johnkok/Amplifier/fw/Drivers/DISPLAY/tm_stm32f4_ili9341.c

/**	
 * |----------------------------------------------------------------------
 * | Copyright (C) Tilen Majerle, 2014
 * | 
 * | This program is free software: you can redistribute it and/or modify
 * | it under the terms of the GNU General Public License as published by
 * | the Free Software Foundation, either version 3 of the License, or
 * | any later version.
 * |  
 * | This program is distributed in the hope that it will be useful,
 * | but WITHOUT ANY WARRANTY; without even the implied warranty of
 * | MERCHANTABILITY or FITNESS FOR A PARTICULAR PURPOSE.  See the
 * | GNU General Public License for more details.
 * | 
 * | You should have received a copy of the GNU General Public License
 * | along with this program.  If not, see <http://www.gnu.org/licenses/>.
 * |----------------------------------------------------------------------
 */
#include "tm_stm32f4_ili9341.h"
#include "stm32f4xx_hal_gpio.h"

extern SPI_HandleTypeDef hspi1;
extern const struct {
  uint32_t   width;
  uint32_t   height;
  uint32_t   bytes_per_pixel; /* 2:RGB16, 3:RGB, 4:RGBA */
  uint8_t 	 pixel_data[];
} vu_image;

/**
 * @brief  Orientation
 * @note   Used private
 */
typedef enum {
	TM_ILI9341_Landscape,
	TM_ILI9341_Portrait
} TM_ILI9341_Orientation;

/**
 * @brief  LCD options
 * @note   Used private
 */
typedef struct {
	uint16_t width;
	uint16_t height;
	TM_ILI9341_Orientation orientation; // 1 = portrait; 0 = landscape
} TM_ILI931_Options_t;

/* Pin definitions */
#define ILI9341_RST_SET				HAL_GPIO_WritePin(ILI9341_RST_PORT, ILI9341_RST_PIN, 1)
#define ILI9341_RST_RESET			HAL_GPIO_WritePin(ILI9341_RST_PORT, ILI9341_RST_PIN, 0)
#define ILI9341_CS_SET				HAL_GPIO_WritePin(ILI9341_CS_PORT, ILI9341_CS_PIN, 1)
#define ILI9341_CS_RESET			HAL_GPIO_WritePin(ILI9341_CS_PORT, ILI9341_CS_PIN, 0)
#define ILI9341_WRX_SET				HAL_GPIO_WritePin(ILI9341_WRX_PORT, ILI9341_WRX_PIN, 1)
#define ILI9341_WRX_RESET			HAL_GPIO_WritePin(ILI9341_WRX_PORT, ILI9341_WRX_PIN, 0)
//#define ILI9341_BL_SET				HAL_GPIO_WritePin(ILI9341_BL_PORT, ILI9341_BL_PIN, 1)
//#define ILI9341_BL_RESET			HAL_GPIO_WritePin(ILI9341_BL_PORT, ILI9341_BL_PIN, 0)

/* Private defines */
#define ILI9341_RESET				0x01
#define ILI9341_SLEEP_OUT			0x11
#define ILI9341_GAMMA				0x26
#define ILI9341_DISPLAY_OFF			0x28
#define ILI9341_DISPLAY_ON			0x29
#define ILI9341_COLUMN_ADDR			0x2A
#define ILI9341_PAGE_ADDR			0x2B
#define ILI9341_GRAM				0x2C
#define ILI9341_MAC					0x36
#define ILI9341_PIXEL_FORMAT		0x3A
#define ILI9341_WDB					0x51
#define ILI9341_WCD					0x53
#define ILI9341_RGB_INTERFACE		0xB0
#define ILI9341_FRC					0xB1
#define ILI9341_BPC					0xB5
#define ILI9341_DFC					0xB6
#define ILI9341_POWER1				0xC0
#define ILI9341_POWER2				0xC1
#define ILI9341_VCOM1				0xC5
#define ILI9341_VCOM2				0xC7
#define ILI9341_POWERA				0xCB
#define ILI9341_POWERB				0xCF
#define ILI9341_PGAMMA				0xE0
#define ILI9341_NGAMMA				0xE1
#define ILI9341_DTCA				0xE8
#define ILI9341_DTCB				0xEA
#define ILI9341_POWER_SEQ			0xED
#define ILI9341_3GAMMA_EN			0xF2
#define ILI9341_INTERFACE			0xF6
#define ILI9341_PRC					0xF7

/* Pin functions */
uint16_t ILI9341_x;
uint16_t ILI9341_y;
TM_ILI931_Options_t ILI9341_Opts;
uint8_t ILI9341_INT_CalledFromPuts = 0;

/* Private functions */
void TM_ILI9341_InitLCD(void);
void TM_ILI9341_SendData(uint8_t data);
void TM_ILI9341_SendCommand(uint8_t data);
void TM_ILI9341_Delay(volatile unsigned int delay);
void TM_ILI9341_SetCursorPosition(uint16_t x1, uint16_t y1, uint16_t x2, uint16_t y2);
void TM_ILI9341_INT_Fill(uint16_t x0, uint16_t y0, uint16_t x1, uint16_t y1, uint16_t color);

void TM_ILI9341_Init() {
	
	/* Init LCD */
//	ILI9341_BL_RESET;

	TM_ILI9341_InitLCD();	
	
	/* Set default settings */
	ILI9341_x = ILI9341_y = 0;
	ILI9341_Opts.width = ILI9341_WIDTH;
	ILI9341_Opts.height = ILI9341_HEIGHT;
	ILI9341_Opts.orientation = TM_ILI9341_Portrait;

	TM_ILI9341_Rotate(TM_ILI9341_Orientation_Landscape_2);
	
	/* Fill with white color */
	TM_ILI9341_Fill(ILI9341_COLOR_BLACK);

//	ILI9341_BL_SET;
}

void TM_ILI9341_InitLCD(void) {
	/* Force reset */
	ILI9341_RST_RESET;
	TM_ILI9341_Delay(20000);
	ILI9341_RST_SET;
	
	/* Delay for RST response */
	TM_ILI9341_Delay(20000);
	
	/* Software reset */
	TM_ILI9341_SendCommand(ILI9341_RESET);
	TM_ILI9341_Delay(50000);
	
	TM_ILI9341_SendCommand(ILI9341_POWERA);
	TM_ILI9341_SendData(0x39);
	TM_ILI9341_SendData(0x2C);
	TM_ILI9341_SendData(0x00);
	TM_ILI9341_SendData(0x34);
	TM_ILI9341_SendData(0x02);
	TM_ILI9341_SendCommand(ILI9341_POWERB);
	TM_ILI9341_SendData(0x00);
	TM_ILI9341_SendData(0xC1);
	TM_ILI9341_SendData(0x30);
	TM_ILI9341_SendCommand(ILI9341_DTCA);
	TM_ILI9341_SendData(0x85);
	TM_ILI9341_SendData(0x00);
	TM_ILI9341_SendData(0x78);
	TM_ILI9341_SendCommand(ILI9341_DTCB);
	TM_ILI9341_SendData(0x00);
	TM_ILI9341_SendData(0x00);
	TM_ILI9341_SendCommand(ILI9341_POWER_SEQ);
	TM_ILI9341_SendData(0x64);
	TM_ILI9341_SendData(0x03);
	TM_ILI9341_SendData(0x12);
	TM_ILI9341_SendData(0x81);
	TM_ILI9341_SendCommand(ILI9341_PRC);
	TM_ILI9341_SendData(0x20);
	TM_ILI9341_SendCommand(ILI9341_POWER1);
	TM_ILI9341_SendData(0x23);
	TM_ILI9341_SendCommand(ILI9341_POWER2);
	TM_ILI9341_SendData(0x10);
	TM_ILI9341_SendCommand(ILI9341_VCOM1);
	TM_ILI9341_SendData(0x3E);
	TM_ILI9341_SendData(0x28);
	TM_ILI9341_SendCommand(ILI9341_VCOM2);
	TM_ILI9341_SendData(0x86);
	TM_ILI9341_SendCommand(ILI9341_MAC);
	TM_ILI9341_SendData(0x48);
	TM_ILI9341_SendCommand(ILI9341_PIXEL_FORMAT);
	TM_ILI9341_SendData(0x55);
	TM_ILI9341_SendCommand(ILI9341_FRC);
	TM_ILI9341_SendData(0x00);
	TM_ILI9341_SendData(0x18);
	TM_ILI9341_SendCommand(ILI9341_DFC);
	TM_ILI9341_SendData(0x08);
	TM_ILI9341_SendData(0x82);
	TM_ILI9341_SendData(0x27);
	TM_ILI9341_SendCommand(ILI9341_3GAMMA_EN);
	TM_ILI9341_SendData(0x00);
	TM_ILI9341_SendCommand(ILI9341_COLUMN_ADDR);
	TM_ILI9341_SendData(0x00);
	TM_ILI9341_SendData(0x00);
	TM_ILI9341_SendData(0x00);
	TM_ILI9341_SendData(0xEF);
	TM_ILI9341_SendCommand(ILI9341_PAGE_ADDR);
	TM_ILI9341_SendData(0x00);
	TM_ILI9341_SendData(0x00);
	TM_ILI9341_SendData(0x01);
	TM_ILI9341_SendData(0x3F);
	TM_ILI9341_SendCommand(ILI9341_GAMMA);
	TM_ILI9341_SendData(0x01);
	TM_ILI9341_SendCommand(ILI9341_PGAMMA);
	TM_ILI9341_SendData(0x0F);
	TM_ILI9341_SendData(0x31);
	TM_ILI9341_SendData(0x2B);
	TM_ILI9341_SendData(0x0C);
	TM_ILI9341_SendData(0x0E);
	TM_ILI9341_SendData(0x08);
	TM_ILI9341_SendData(0x4E);
	TM_ILI9341_SendData(0xF1);
	TM_ILI9341_SendData(0x37);
	TM_ILI9341_SendData(0x07);
	TM_ILI9341_SendData(0x10);
	TM_ILI9341_SendData(0x03);
	TM_ILI9341_SendData(0x0E);
	TM_ILI9341_SendData(0x09);
	TM_ILI9341_SendData(0x00);
	TM_ILI9341_SendCommand(ILI9341_NGAMMA);
	TM_ILI9341_SendData(0x00);
	TM_ILI9341_SendData(0x0E);
	TM_ILI9341_SendData(0x14);
	TM_ILI9341_SendData(0x03);
	TM_ILI9341_SendData(0x11);
	TM_ILI9341_SendData(0x07);
	TM_ILI9341_SendData(0x31);
	TM_ILI9341_SendData(0xC1);
	TM_ILI9341_SendData(0x48);
	TM_ILI9341_SendData(0x08);
	TM_ILI9341_SendData(0x0F);
	TM_ILI9341_SendData(0x0C);
	TM_ILI9341_SendData(0x31);
	TM_ILI9341_SendData(0x36);
	TM_ILI9341_SendData(0x0F);
	TM_ILI9341_SendCommand(ILI9341_SLEEP_OUT);

	TM_ILI9341_Delay(1000000);

	TM_ILI9341_SendCommand(ILI9341_DISPLAY_ON);
	TM_ILI9341_SendCommand(ILI9341_GRAM);
}

void TM_ILI9341_DisplayOn(void) {
	TM_ILI9341_SendCommand(ILI9341_DISPLAY_ON);
}

void TM_ILI9341_DisplayOff(void) {
	TM_ILI9341_SendCommand(ILI9341_DISPLAY_OFF);
}

void TM_ILI9341_SendCommand(uint8_t data) {
	ILI9341_WRX_RESET;
	ILI9341_CS_RESET;
	HAL_SPI_Transmit(&hspi1, &data, 1, 5);
	//HAL_SPI_Transmit_DMA(&hspi1, &data, 1);
	ILI9341_CS_SET;
}

void TM_ILI9341_SendData(uint8_t data) {
	ILI9341_WRX_SET;
	ILI9341_CS_RESET;
	HAL_SPI_Transmit(&hspi1, &data, 1, 5);
	//HAL_SPI_Transmit_DMA(&hspi1, &data, 1);
	ILI9341_CS_SET;
}

void TM_ILI9341_DrawPixel(uint16_t x, uint16_t y, uint32_t color) {
	TM_ILI9341_SetCursorPosition(x, y, x, y);

	TM_ILI9341_SendCommand(ILI9341_GRAM);
	TM_ILI9341_SendData(color >> 8);
	TM_ILI9341_SendData(color & 0xFF);
}


void TM_ILI9341_SetCursorPosition(uint16_t x1, uint16_t y1, uint16_t x2, uint16_t y2) {
	TM_ILI9341_SendCommand(ILI9341_COLUMN_ADDR);
	TM_ILI9341_SendData(x1 >> 8);
	TM_ILI9341_SendData(x1 & 0xFF);
	TM_ILI9341_SendData(x2 >> 8);
	TM_ILI9341_SendData(x2 & 0xFF);

	TM_ILI9341_SendCommand(ILI9341_PAGE_ADDR);
	TM_ILI9341_SendData(y1 >> 8);
	TM_ILI9341_SendData(y1 & 0xFF);
	TM_ILI9341_SendData(y2 >> 8);
	TM_ILI9341_SendData(y2 & 0xFF);
}

void TM_ILI9341_Fill(uint32_t color) {
	/* Fill entire screen */
	TM_ILI9341_INT_Fill(0, 0, ILI9341_Opts.width, ILI9341_Opts.height, color);
}

void TM_ILI9341_INT_Fill(uint16_t x0, uint16_t y0, uint16_t x1, uint16_t y1, uint16_t color) {
	uint32_t pixels_count;
	uint16_t *temp;
	uint32_t i;

	/* Calculate pixels count */
	pixels_count = (x1 - x0) * (y1 - y0);

	if (pixels_count > 64) {
		temp = (uint16_t *)malloc((size_t)(128 * sizeof(uint16_t)));
		if (!temp) return;
		memset(temp, color, 64);
	}
	else{
		temp = (uint16_t *)malloc((size_t)pixels_count);
		if (!temp) return;
		for (i=0 ; i < pixels_count ; i++) {
	        temp[i] = color;
		}
	}

	/* Set cursor position */
	TM_ILI9341_SetCursorPosition(x0, y0, x1, y1);

	/* Set command for GRAM data */
	TM_ILI9341_SendCommand(ILI9341_GRAM);
	
	/* Send everything */
	ILI9341_WRX_SET;
	
	//hspi1.Init.DataSize = SPI_DATASIZE_16BIT;
	//HAL_SPI_Init(&hspi1);

	while (pixels_count) {
		if (pixels_count > 64) {
			ILI9341_CS_RESET;
			HAL_SPI_Transmit(&hspi1, (uint8_t *)temp, 128, 100);
			//HAL_SPI_Transmit_DMA(&hspi1, (uint8_t *)temp, 128);
			//pixels_count -= 1024;
			pixels_count -= 64;
			ILI9341_CS_SET;
		}
		else {
			ILI9341_CS_RESET;
			HAL_SPI_Transmit(&hspi1, (uint8_t *)temp, pixels_count, 100);
			//HAL_SPI_Transmit_DMA(&hspi1, (uint8_t *)temp, pixels_count);
			pixels_count = 0;
			ILI9341_CS_SET;
		}
	}

	//hspi1.Init.DataSize = SPI_DATASIZE_8BIT;
	//HAL_SPI_Init(&hspi1);

	free(temp);
}

void TM_ILI9341_Delay(volatile unsigned int delay) {
	for (; delay != 0; delay--); 
}

void TM_ILI9341_Rotate(TM_ILI9341_Orientation_t orientation) {
	TM_ILI9341_SendCommand(ILI9341_MAC);
	if (orientation == TM_ILI9341_Orientation_Portrait_1) {
		TM_ILI9341_SendData(0x58);
	} else if (orientation == TM_ILI9341_Orientation_Portrait_2) {
		TM_ILI9341_SendData(0x88);
	} else if (orientation == TM_ILI9341_Orientation_Landscape_1) {
		TM_ILI9341_SendData(0x28);
	} else if (orientation == TM_ILI9341_Orientation_Landscape_2) {
		TM_ILI9341_SendData(0xE8);
	}
	
	if (orientation == TM_ILI9341_Orientation_Portrait_1 || orientation == TM_ILI9341_Orientation_Portrait_2) {
		ILI9341_Opts.width = ILI9341_WIDTH;
		ILI9341_Opts.height = ILI9341_HEIGHT;
		ILI9341_Opts.orientation = TM_ILI9341_Portrait;
	} else {
		ILI9341_Opts.width = ILI9341_HEIGHT;
		ILI9341_Opts.height = ILI9341_WIDTH;
		ILI9341_Opts.orientation = TM_ILI9341_Landscape;
	}
}

void TM_ILI9341_Puts(uint16_t x, uint16_t y, char *str, TM_FontDef_t *font, uint32_t foreground, uint32_t background) {
	uint16_t startX = x;
	
	/* Set X and Y coordinates */
	ILI9341_x = x;
	ILI9341_y = y;
	
	while (*str) {
		/* New line */
		if (*str == '\n') {
			ILI9341_y += font->FontHeight + 1;
			/* if after \n is also \r, than go to the left of the screen */
			if (*(str + 1) == '\r') {
				ILI9341_x = 0;
				str++;
			} else {
				ILI9341_x = startX;
			}
			str++;
			continue;
		} else if (*str == '\r') {
			str++;
			continue;
		}
		
		/* Put character to LCD */
		TM_ILI9341_Putc(ILI9341_x, ILI9341_y, *str++, font, foreground, background);
	}
}

void TM_ILI9341_GetStringSize(char *str, TM_FontDef_t *font, uint16_t *width, uint16_t *height) {
	uint16_t w = 0;
	*height = font->FontHeight;
	while (*str++) {
		w += font->FontWidth;
	}
	*width = w;
}

void TM_ILI9341_Putc(uint16_t x, uint16_t y, char c, TM_FontDef_t *font, uint32_t foreground, uint32_t background) {
	uint32_t i, b, j;
	/* Set coordinates */
	ILI9341_x = x;
	ILI9341_y = y;
	
	if ((ILI9341_x + font->FontWidth) > ILI9341_Opts.width) {
		/* If at the end of a line of display, go to new line and set x to 0 position */
		ILI9341_y += font->FontHeight;
		ILI9341_x = 0;
	}
	
	/* Draw rectangle for background */
	TM_ILI9341_INT_Fill(ILI9341_x, ILI9341_y, ILI9341_x + font->FontWidth, ILI9341_y + font->FontHeight, background);
	
	/* Draw font data */
	for (i = 0; i < font->FontHeight; i++) {
		b = font->data[(c - 32) * font->FontHeight + i];
		for (j = 0; j < font->FontWidth; j++) {
			if ((b << j) & 0x8000) {
				TM_ILI9341_DrawPixel(ILI9341_x + j, (ILI9341_y + i), foreground);
			}
		}
	}
	
	/* Set new pointer */
	ILI9341_x += font->FontWidth;
}


void TM_ILI9341_DrawLine(uint16_t x0, uint16_t y0, uint16_t x1, uint16_t y1, uint32_t color) {
	/* Code by dewoller: https://github.com/dewoller */
	
	int16_t dx, dy, sx, sy, err, e2; 	
	uint16_t tmp;
	
	/* Check for overflow */
	if (x0 >= ILI9341_Opts.width) {
		x0 = ILI9341_Opts.width - 1;
	}
	if (x1 >= ILI9341_Opts.width) {
		x1 = ILI9341_Opts.width - 1;
	}
	if (y0 >= ILI9341_Opts.height) {
		y0 = ILI9341_Opts.height - 1;
	}
	if (y1 >= ILI9341_Opts.height) {
		y1 = ILI9341_Opts.height - 1;
	}
	
	/* Check correction */
	if (x0 > x1) {
		tmp = x0;
		x0 = x1;
		x1 = tmp;
	}
	if (y0 > y1) {
		tmp = y0;
		y0 = y1;
		y1 = tmp;
	}
	
	dx = x1 - x0;
	dy = y1 - y0;
	
	/* Vertical or horizontal line */
	if (dx == 0 || dy == 0) {
		TM_ILI9341_INT_Fill(x0, y0, x1, y1, color);
		return;
	}
	
	sx = (x0 < x1) ? 1 : -1; 
	sy = (y0 < y1) ? 1 : -1; 
	err = ((dx > dy) ? dx : -dy) / 2; 

	while (1) {
		TM_ILI9341_DrawPixel(x0, y0, color); 
		if (x0 == x1 && y0 == y1) {
			break;
		}
		e2 = err; 
		if (e2 > -dx) {
			err -= dy;
			x0 += sx;
		} 
		if (e2 < dy) {
			err += dx;
			y0 += sy;
		} 
	}
}

void TM_ILI9341_DrawRectangle(uint16_t x0, uint16_t y0, uint16_t x1, uint16_t y1, uint32_t color) {
	TM_ILI9341_DrawLine(x0, y0, x1, y0, color); //Top
	TM_ILI9341_DrawLine(x0, y0, x0, y1, color);	//Left
	TM_ILI9341_DrawLine(x1, y0, x1, y1, color);	//Right
	TM_ILI9341_DrawLine(x0, y1, x1, y1, color);	//Bottom
}

void TM_ILI9341_DrawFilledRectangle(uint16_t x0, uint16_t y0, uint16_t x1, uint16_t y1, uint32_t color) {	
	uint16_t tmp;
	
	/* Check correction */
	if (x0 > x1) {
		tmp = x0;
		x0 = x1;
		x1 = tmp;
	}
	if (y0 > y1) {
		tmp = y0;
		y0 = y1;
		y1 = tmp;
	}
	
	/* Fill rectangle */
	TM_ILI9341_INT_Fill(x0, y0, x1, y1, color);
	
	/* CS HIGH back */
	ILI9341_CS_SET;
}

void TM_ILI9341_DrawCircle(int16_t x0, int16_t y0, int16_t r, uint32_t color) {
	int16_t f = 1 - r;
	int16_t ddF_x = 1;
	int16_t ddF_y = -2 * r;
	int16_t x = 0;
	int16_t y = r;

    TM_ILI9341_DrawPixel(x0, y0 + r, color);
    TM_ILI9341_DrawPixel(x0, y0 - r, color);
    TM_ILI9341_DrawPixel(x0 + r, y0, color);
    TM_ILI9341_DrawPixel(x0 - r, y0, color);

    while (x < y) {
        if (f >= 0) {
            y--;
            ddF_y += 2;
            f += ddF_y;
        }
        x++;
        ddF_x += 2;
        f += ddF_x;

        TM_ILI9341_DrawPixel(x0 + x, y0 + y, color);
        TM_ILI9341_DrawPixel(x0 - x, y0 + y, color);
        TM_ILI9341_DrawPixel(x0 + x, y0 - y, color);
        TM_ILI9341_DrawPixel(x0 - x, y0 - y, color);

        TM_ILI9341_DrawPixel(x0 + y, y0 + x, color);
        TM_ILI9341_DrawPixel(x0 - y, y0 + x, color);
        TM_ILI9341_DrawPixel(x0 + y, y0 - x, color);
        TM_ILI9341_DrawPixel(x0 - y, y0 - x, color);
    }
}

void TM_ILI9341_DrawFilledCircle(int16_t x0, int16_t y0, int16_t r, uint32_t color) {
	int16_t f = 1 - r;
	int16_t ddF_x = 1;
	int16_t ddF_y = -2 * r;
	int16_t x = 0;
	int16_t y = r;

    TM_ILI9341_DrawPixel(x0, y0 + r, color);
    TM_ILI9341_DrawPixel(x0, y0 - r, color);
    TM_ILI9341_DrawPixel(x0 + r, y0, color);
    TM_ILI9341_DrawPixel(x0 - r, y0, color);
    TM_ILI9341_DrawLine(x0 - r, y0, x0 + r, y0, color);

    while (x < y) {
        if (f >= 0) {
            y--;
            ddF_y += 2;
            f += ddF_y;
        }
        x++;
        ddF_x += 2;
        f += ddF_x;

        TM_ILI9341_DrawLine(x0 - x, y0 + y, x0 + x, y0 + y, color);
        TM_ILI9341_DrawLine(x0 + x, y0 - y, x0 - x, y0 - y, color);

        TM_ILI9341_DrawLine(x0 + y, y0 + x, x0 - y, y0 + x, color);
        TM_ILI9341_DrawLine(x0 + y, y0 - x, x0 - y, y0 - x, color);
    }
}

void TM_ILI9341_DrawImage(uint16_t x0, uint16_t y0, uint16_t x1, uint16_t y1, uint32_t imgId) {
    uint32_t i = 0;

	/* Set cursor position */
	TM_ILI9341_SetCursorPosition(45, 0, 285-1, 240-1);

	/* Set command for GRAM data */
	TM_ILI9341_SendCommand(ILI9341_GRAM);

	switch(imgId){
	  case 0:
		for (i = 0; i < vu_image.height * vu_image.width * vu_image.bytes_per_pixel; i = i + 2) {
			TM_ILI9341_SendData(vu_image.pixel_data[i+1]);
			TM_ILI9341_SendData(vu_image.pixel_data[i]);
		}
	 	break;
	}
}
