johnkok/Amplifier/fw/Drivers/DISPLAY/vu.c

/* GIMP RGB C-Source image dump (vu.c) */

const struct {
  unsigned int 	 width;
  unsigned int 	 height;
  unsigned int 	 bytes_per_pixel; /* 2:RGB16, 3:RGB, 4:RGBA */ 
  unsigned char	 pixel_data[240 * 240 * 2 + 1];
} vu_image = {
  240, 240, 2,
  "\242\020\242\020\242\020\242\020\242\020\242\020\242\020\242\020\242\020\242\020\242"
  "\020\242\020\242\020\242\020\242\020\242\020\242\020\242\020\242\020\242\020\242\020"
  "\242\020\242\020\242\020\242\020\243\020\243\020\243\020\242\020\242\020\242\020\243"
  "\020\243\020\243\020\243\020\243\020\243\030\243\020\243\020\243\020\243\020\243\020"
  "\242\020\242\020\302\020\242\020\242\020\242\020\242\020\242\020\242\020\242\020\242"
  "\020\242\020\242\020\242\020\242\020\242\020\242\020\242\020\242\020\242\020\242\020"
  "\242\020\242\020\242\020\242\020\243\020\242\030\302\030\242\020\242\020\242\020\243"
  "\020\243\020\242\030\242\030\003!\004!E)D)D)D)D)#)#!\004!\004!\004!\003!B\071\302\071\241A"
  "!Z`b\301r\340\202\201\202\201\202\300\202\300\202\000\223\000\223\000\223\000\223"
  "\200\212\000\223\000\223\000\223\040\213\040\213\000\223\000\223\040\213\040\213\040\213"
  "\040\213\000\223\000\223\000\223\000\223\000\223\000\223\000\223\000\223\000\223\000\223\000\223"
  "\000\223\040\213\040\213\040\213\200\233`\243\200\233\200\233`\243`\243\200\233"
  "\200\233\200\233\200\233\040\213\040\213\340\202@j!Z\300IA\071C)#)\002!D)E)\004"
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
  "\000\000\301r%\325\244\233\001\000B\071\305\274\"\376\"\376\001\376\"\376\"\376\"\376"
  "\"\376c\376g\376e\376\346\365'\356\307\223DRI\356c\376&\376e\376F\366f\376"
  "F\376G\376G\376F\376F\376F\376f\376&\376f\376F\366f\376'\356\347\254\346"
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
